VincePrints/cadet_yoke_v2/images/20210520_19434253453453952.jpg

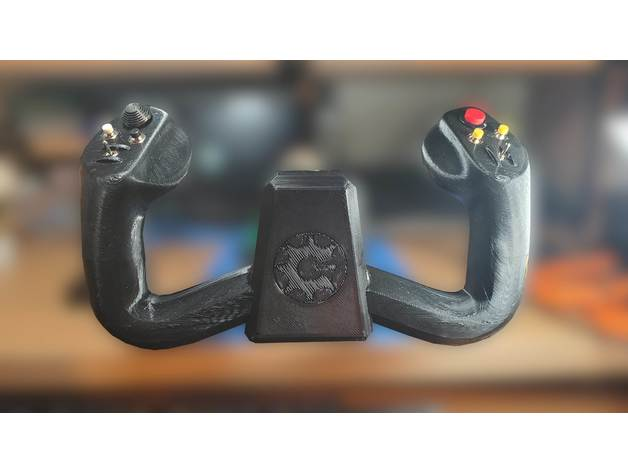
images/20210520_19434253453453952.jpg
