VincePrints/cadet_yoke_v2/images/Base_Front.png

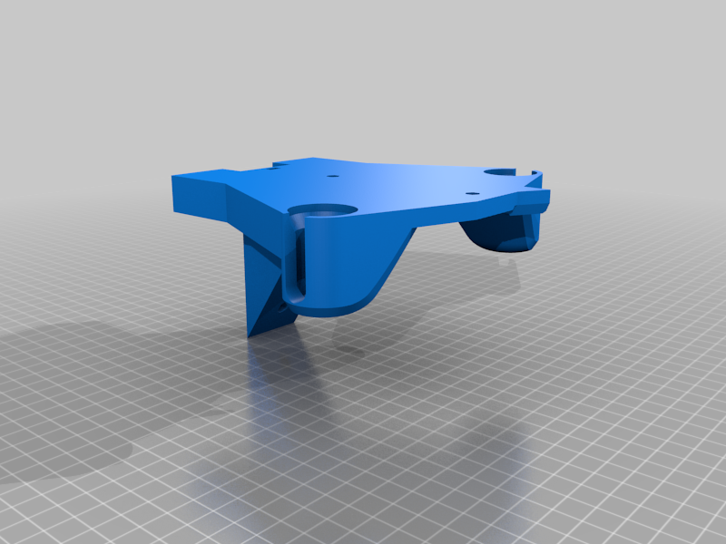
images/Base_Front.png
