VincePrints/cadet_yoke_v2/images/Base_Rear.png

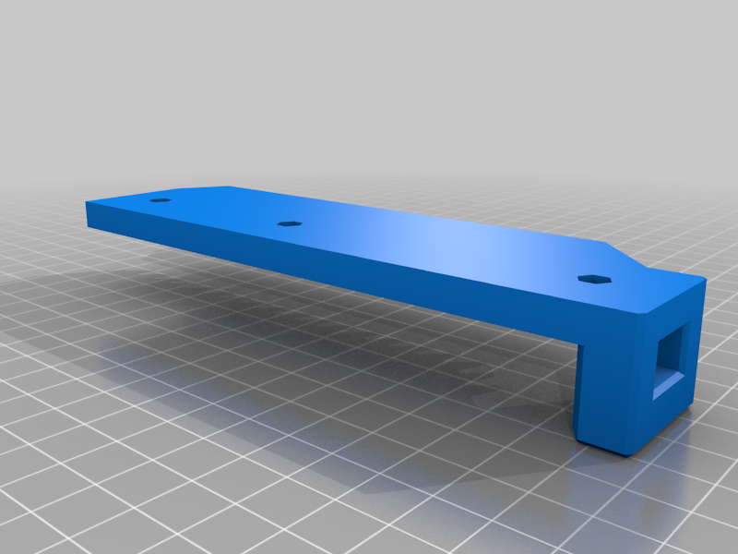
images/Base_Rear.png
