VincePrints/cadet_yoke_v2/images/Centering_Collar.png

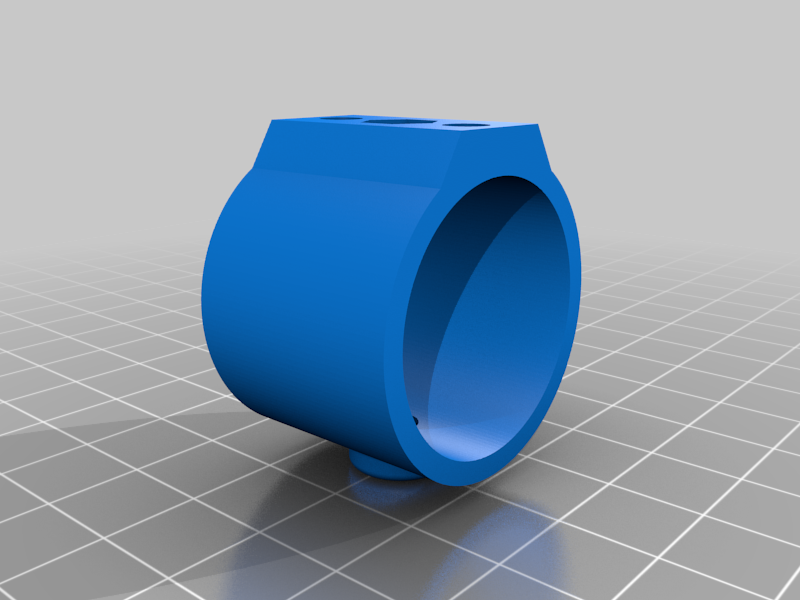
images/Centering_Collar.png
