VincePrints/cadet_yoke_v2/images/Console_Back.png

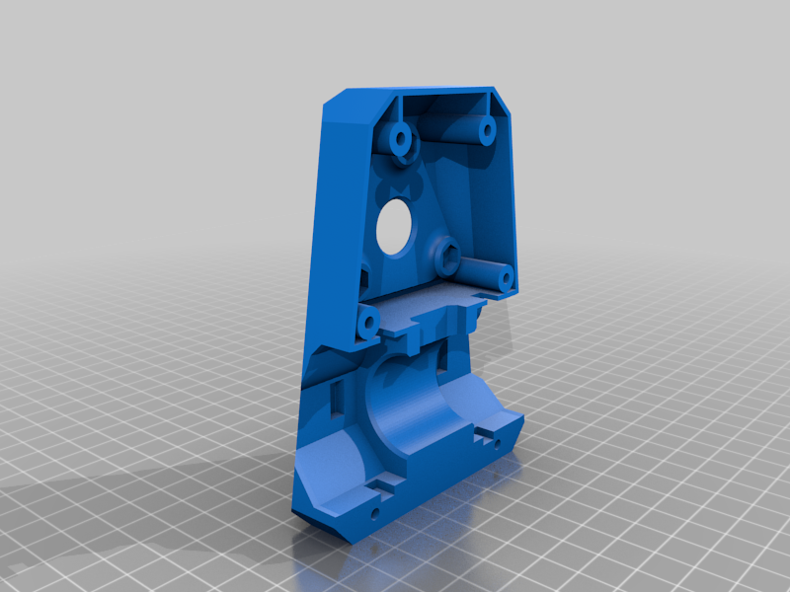
images/Console_Back.png
