VincePrints/cadet_yoke_v2/images/Controller_LB.png

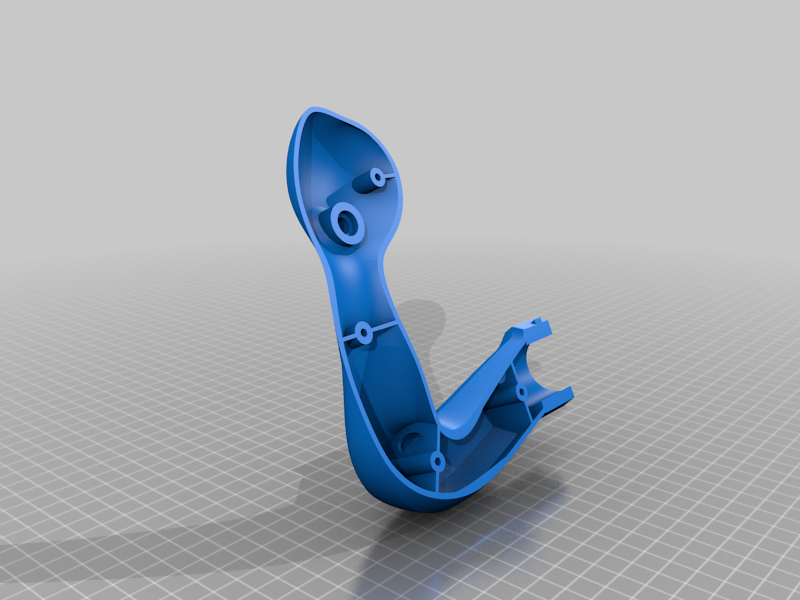
images/Controller_LB.png
