VincePrints/cadet_yoke_v2/images/Hat_Switch_Mount.png

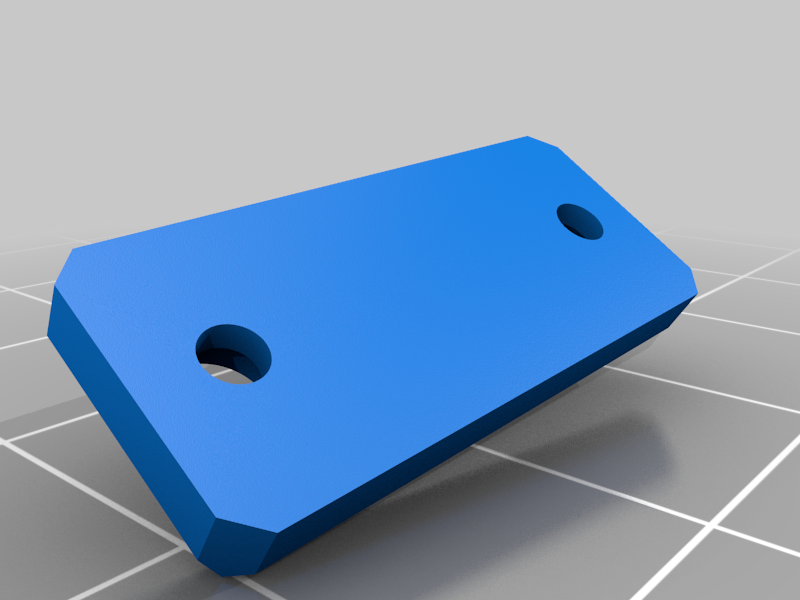
images/Hat_Switch_Mount.png
