VincePrints/cadet_yoke_v2/images/Hat_Switch_Topper.png

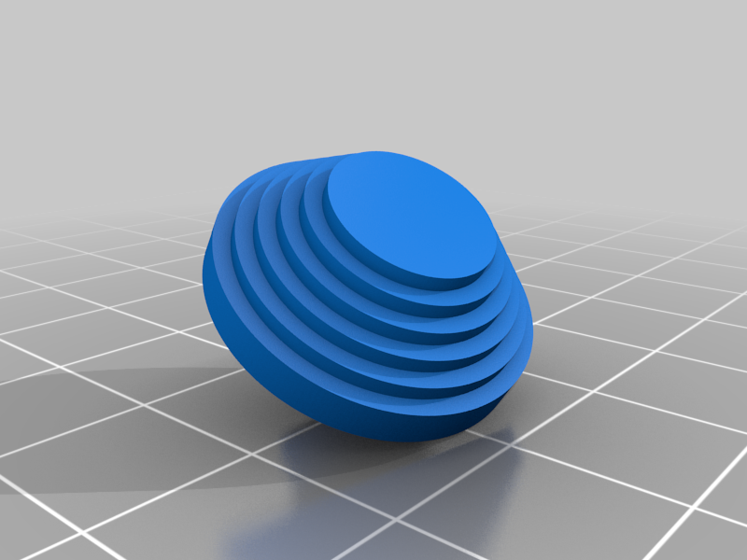
images/Hat_Switch_Topper.png
