VincePrints/cadet_yoke_v2/images/Helical_Roll_Gear_21R.png

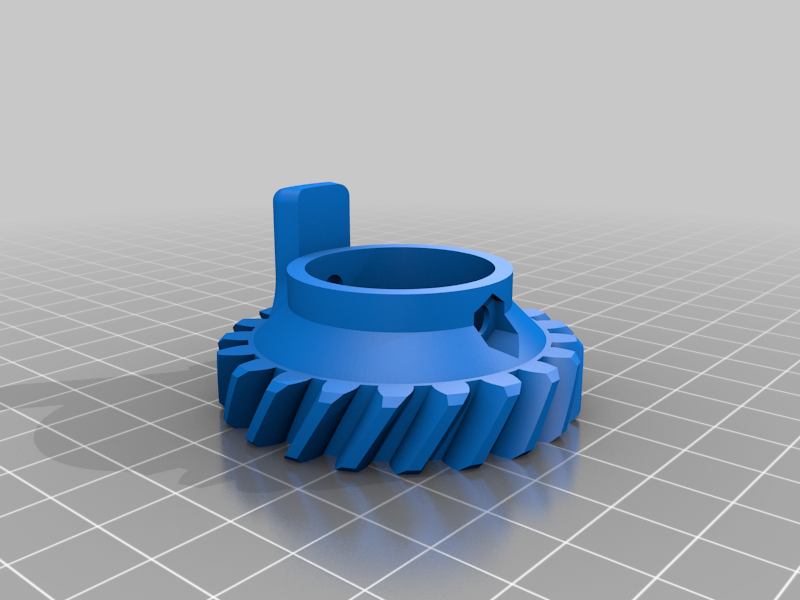
images/Helical_Roll_Gear_21R.png
