VincePrints/cadet_yoke_v2/images/Helical_Roll_Gear__14L.png

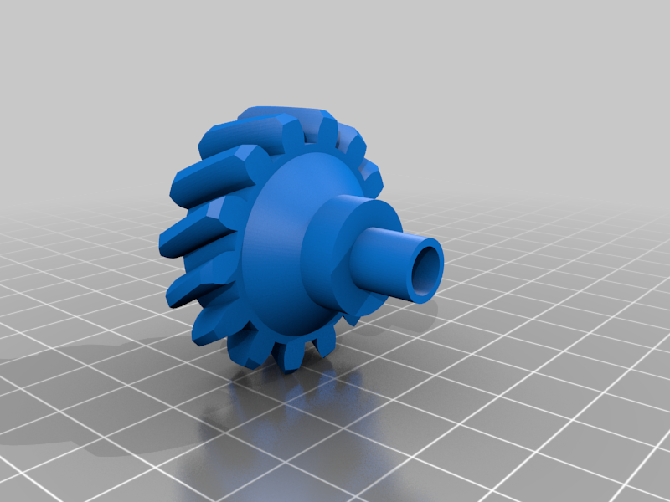
images/Helical_Roll_Gear__14L.png
