VincePrints/cadet_yoke_v2/images/Linear_Rail_Mount.png

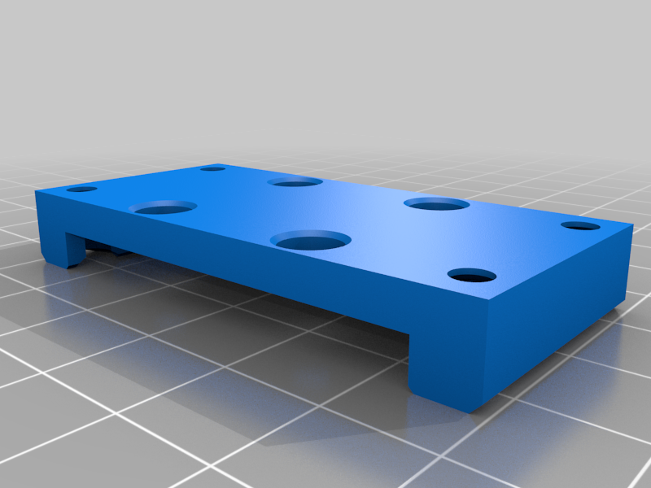
images/Linear_Rail_Mount.png
