VincePrints/cadet_yoke_v2/3D files/Console_Back.stl

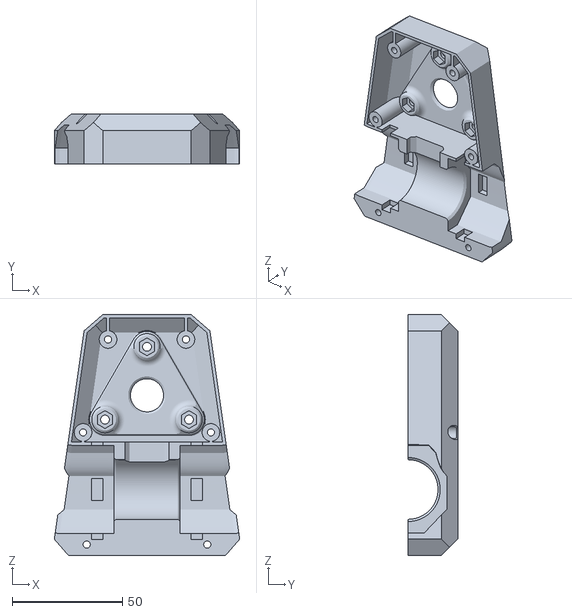
[picture p31: CAD file, 2023-11-08]
3D files/Console_Back.stl
84.1 x 22.5 x 109.3
