VincePrints/cadet_yoke_v2/3D files/Electronics_Housing_Lid.stl

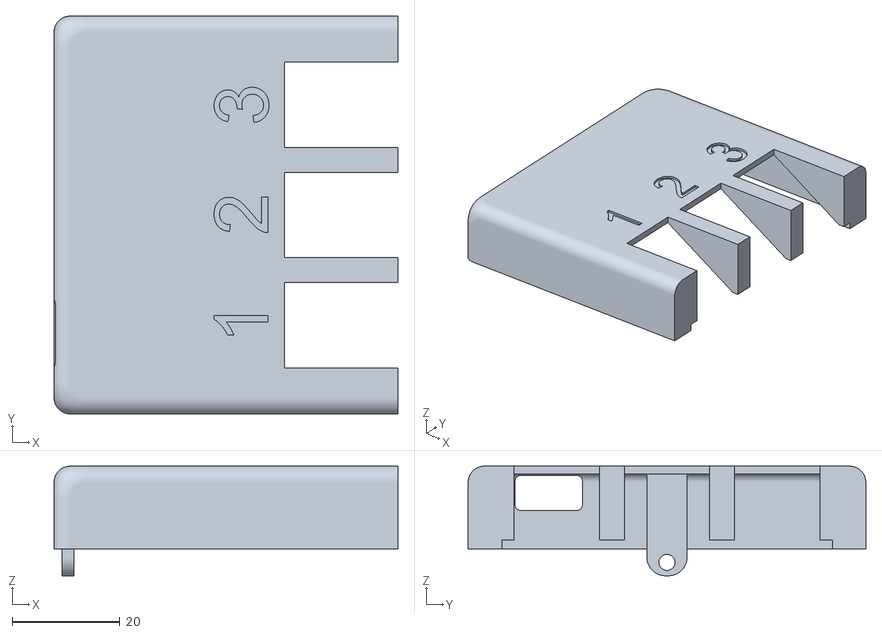
[picture p32: CAD file, 2023-11-08]
3D files/Electronics_Housing_Lid.stl
64.0 x 74.0 x 20.4
