VincePrints/cadet_yoke_v2/3D files/Base_Guide.stl

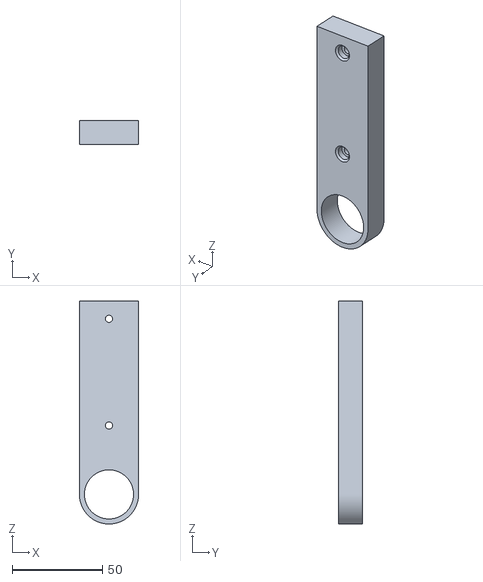
[picture p33: CAD file, 2023-11-08]
3D files/Base_Guide.stl
32.9 x 13.2 x 123.8
