VincePrints/cadet_yoke_v2/3D files/Collar_Clip.stl

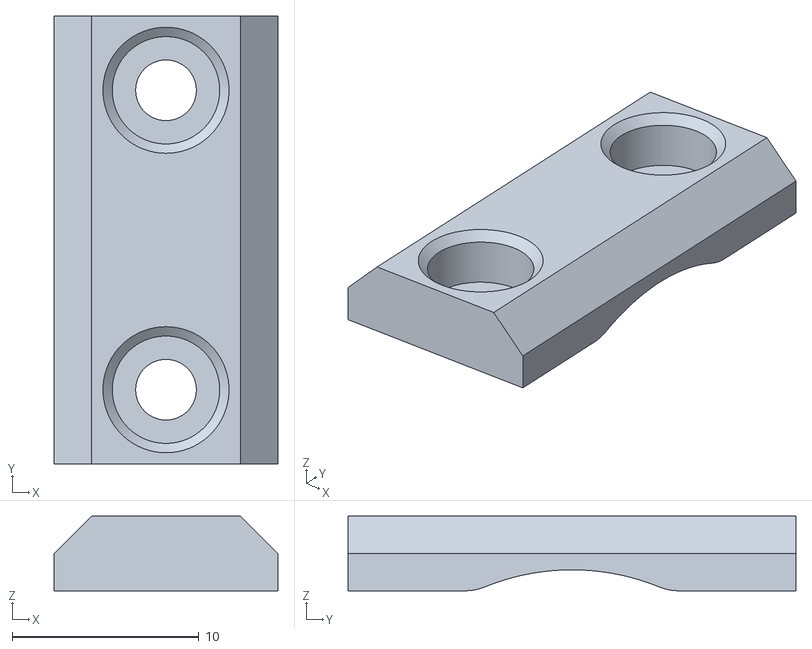
[picture p34: CAD file, 2023-11-08]
3D files/Collar_Clip.stl
12.0 x 24.0 x 4.00
