VincePrints/cadet_yoke_v2/3D files/Electronics_Housing_Base.stl

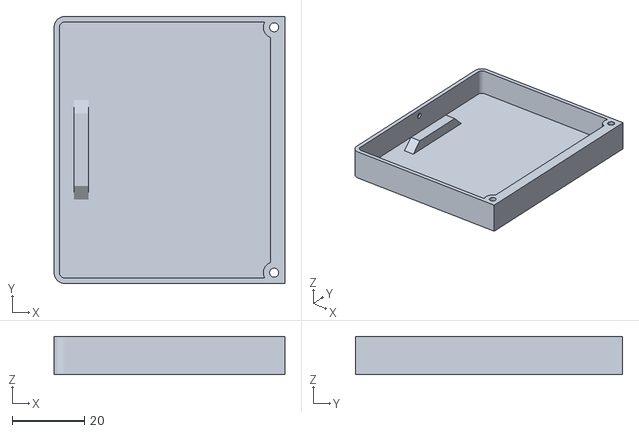
[picture p35: CAD file, 2023-11-08]
3D files/Electronics_Housing_Base.stl
64.0 x 74.0 x 10.7
